arbalet-project/arbadoc/graphical_elements/background.JPG

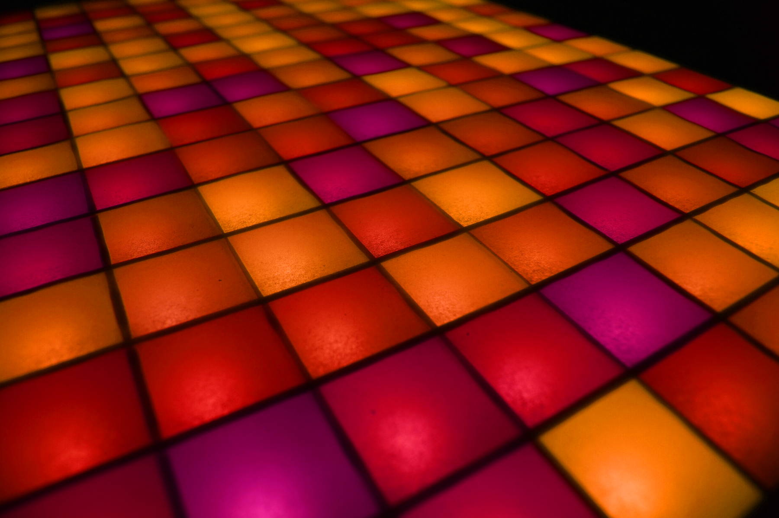
graphical_elements/background.JPG
