arbalet-project/arbadoc/graphical_elements/background_wide.jpg

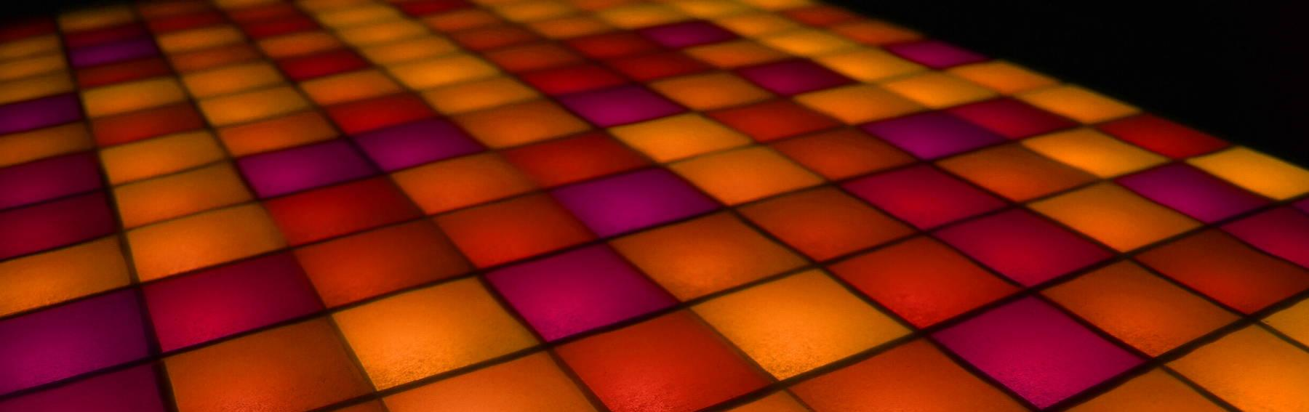
graphical_elements/background_wide.jpg
