arbalet-project/arbadoc/pics/collaborative_tetris.jpeg

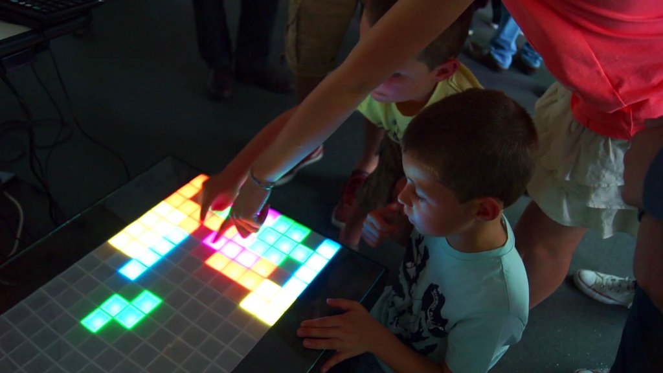
pics/collaborative_tetris.jpeg
