arbalet-project/arbadoc/pics/lights_hero.jpg

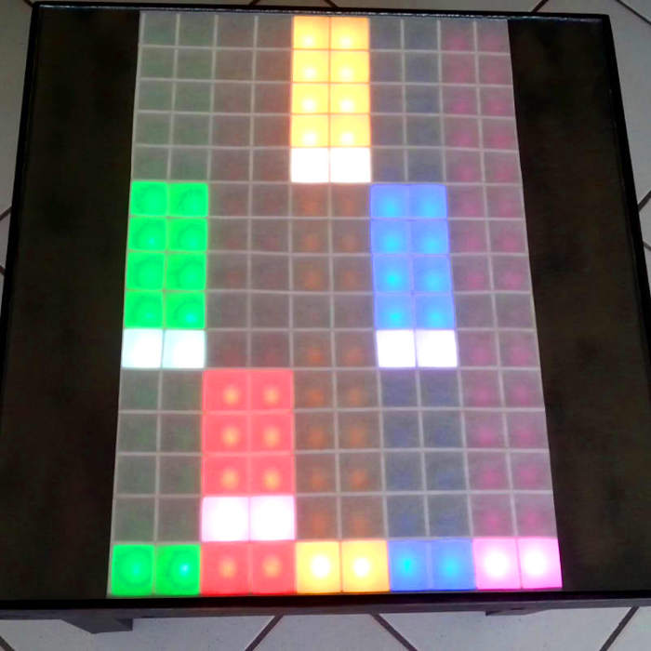
pics/lights_hero.jpg
