arbalet-project/arbadoc/pics/lights_hero_florian.jpg

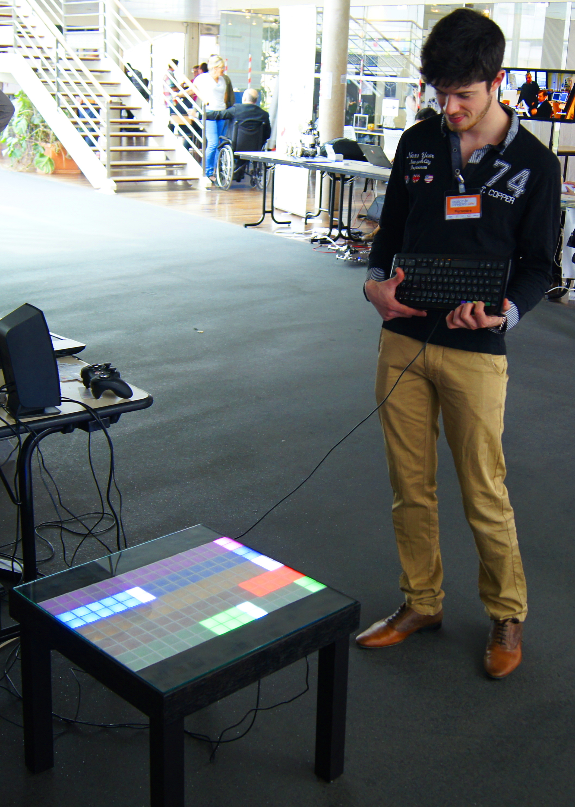
pics/lights_hero_florian.jpg
