arbalet-project/arbadoc/assembly_guidelines/lack/cad/Arbalet_TABLE_ASM.SLDASM

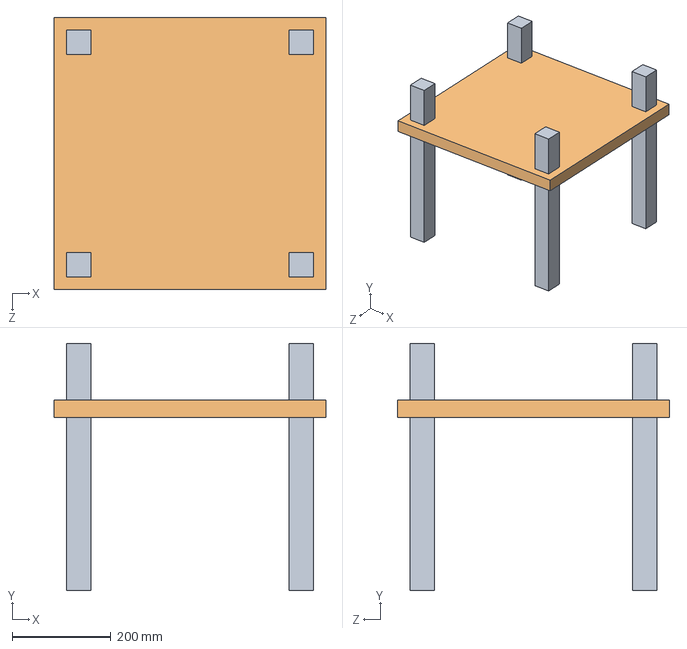
[picture p14: CAD file, 2015-10-09]
assembly_guidelines/lack/cad/Arbalet_TABLE_ASM.SLDASM
550.0 x 500.0 x 550.0 mm
Arbalet_TABLE_Tray
Arbalet_TABLE_LEG x 4
