arbalet-project/arbadoc/assembly_guidelines/lava/cad/host_box_grid_legs.fcstd

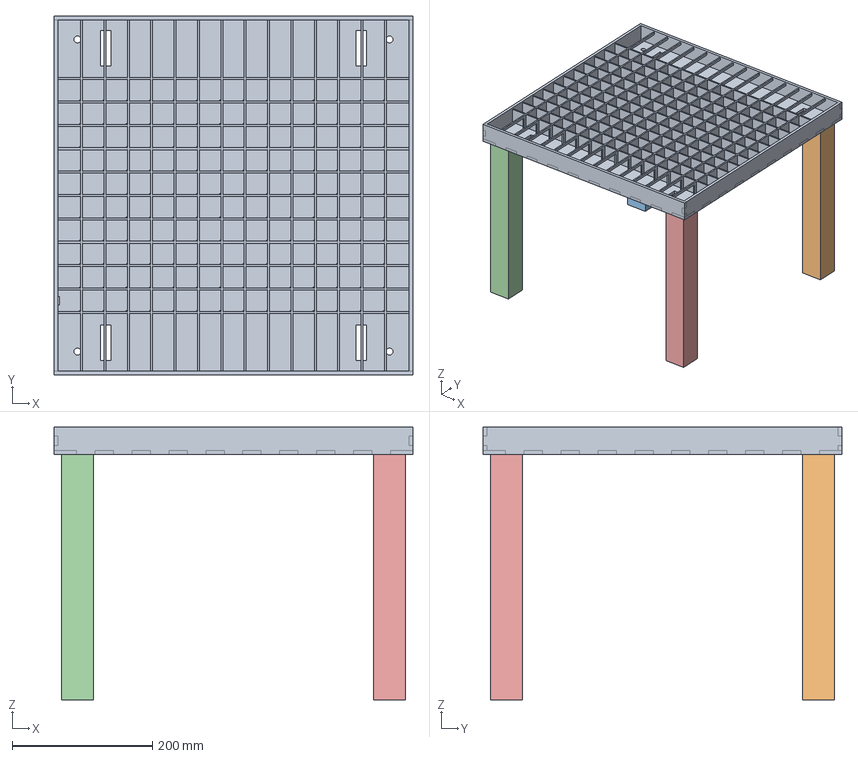
[picture p24: CAD file, 2016-04-23]
assembly_guidelines/lava/cad/host_box_grid_legs.fcstd
512.0 x 512.0 x 389.0 mm
host_box_grid_01
leg_01
leg_02
leg_03
leg_04
