arbalet-project/arbadoc/assembly_guidelines/lava/cad/leg.fcstd

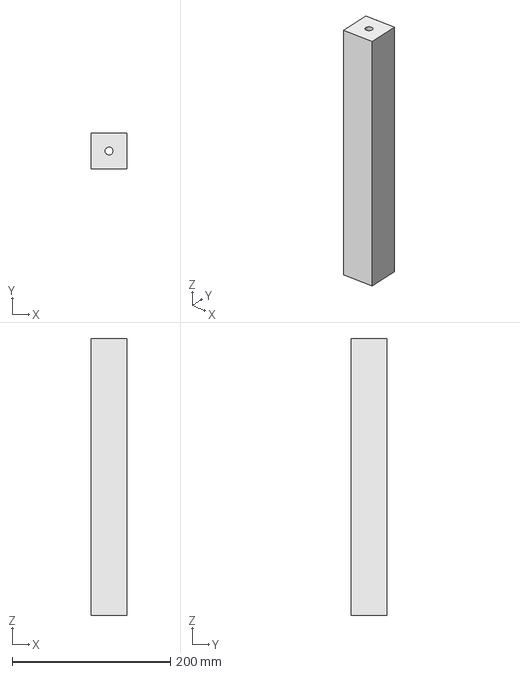
[picture p25: CAD file, 2016-03-13]
assembly_guidelines/lava/cad/leg.fcstd
45.0 x 45.0 x 350.0 mm
