arbalet-project/arbadoc/assembly_guidelines/lack/cad/Arbalet_GRID_Cover.SLDPRT

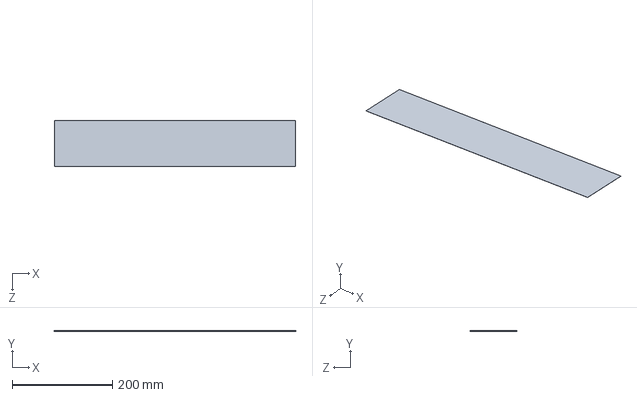
[picture p26: CAD file, 2015-10-09]
assembly_guidelines/lack/cad/Arbalet_GRID_Cover.SLDPRT
480.0 x 0.2 x 92.5 mm
