arbalet-project/arbadoc/assembly_guidelines/lava/cad/strip_333.fcstd

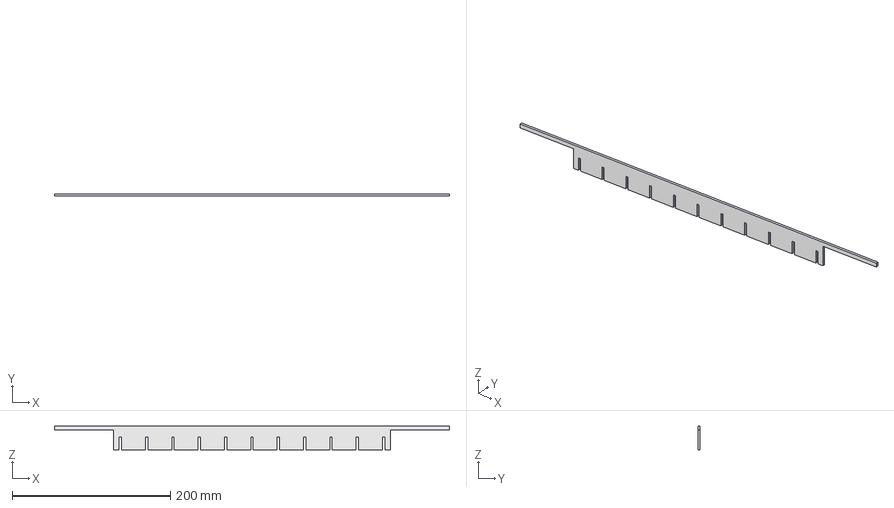
[picture p27: CAD file, 2016-03-13]
assembly_guidelines/lava/cad/strip_333.fcstd
500.0 x 3.00 x 30.0 mm
