arbalet-project/arbadoc/assembly_guidelines/lava/cad/strips_333.fcstd

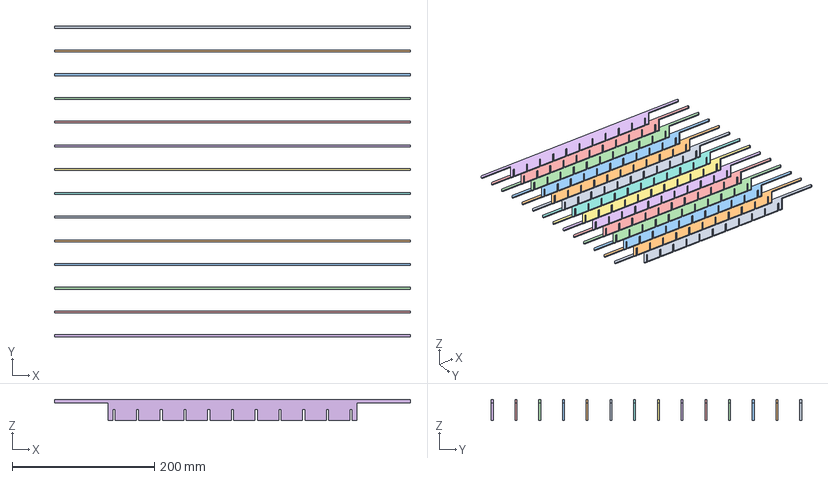
[picture p28: CAD file, 2016-03-13]
assembly_guidelines/lava/cad/strips_333.fcstd
500.0 x 436.3 x 30.0 mm
strip_333_01
strip_333_02
strip_333_03
strip_333_04
strip_333_05
strip_333_06
strip_333_07
strip_333_08
strip_333_09
strip_333_10
strip_333_11
strip_333_12
strip_333_13
strip_333_14
