arbalet-project/arbadoc/assembly_guidelines/lack/cad/Arbalet_GRID_Diffuser.SLDPRT

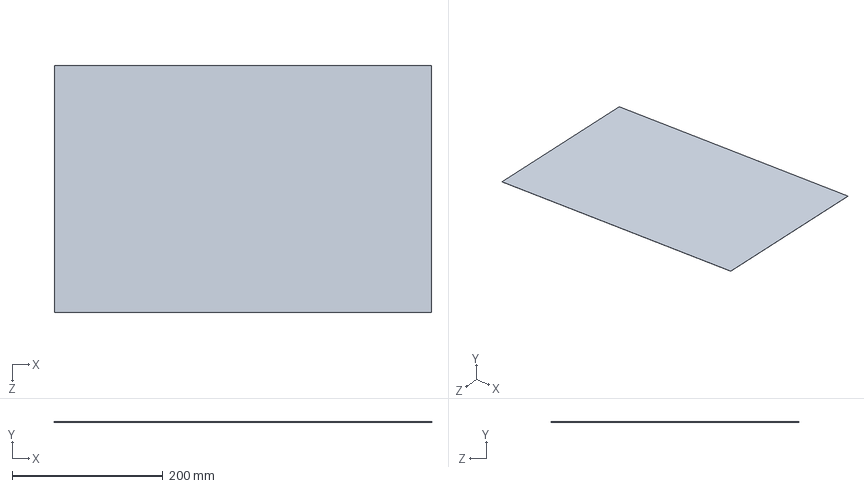
[picture p29: CAD file, 2015-10-09]
assembly_guidelines/lack/cad/Arbalet_GRID_Diffuser.SLDPRT
500.0 x 0.2 x 328.0 mm
