arbalet-project/arbadoc/assembly_guidelines/lava/cad/side_333.fcstd

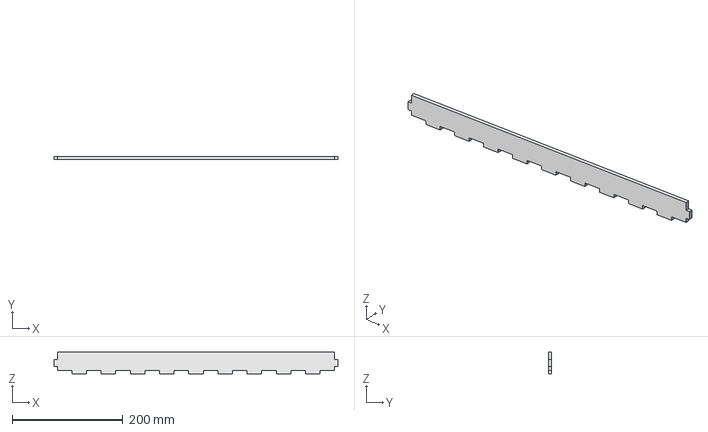
[picture p30: CAD file, 2016-03-13]
assembly_guidelines/lava/cad/side_333.fcstd
512.0 x 6.00 x 39.0 mm
