arbalet-project/arbadoc/assembly_guidelines/lack/cad/Arbalet_UPPER_TRAY_Frame.SLDPRT

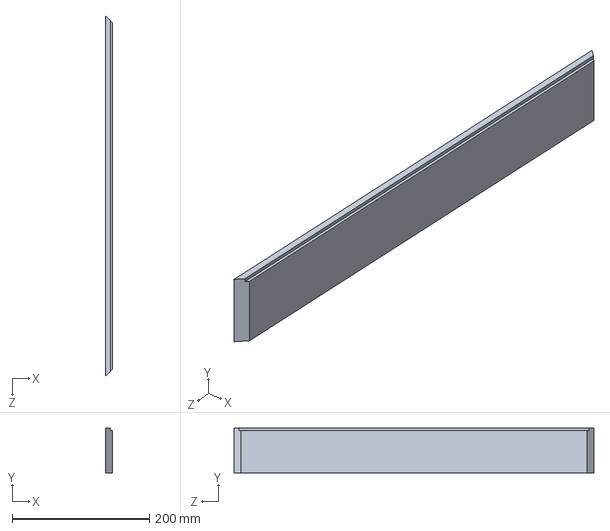
[picture p31: CAD file, 2015-10-09]
assembly_guidelines/lack/cad/Arbalet_UPPER_TRAY_Frame.SLDPRT
10.0 x 65.0 x 525.0 mm
