arbalet-project/arbadoc/assembly_guidelines/lack/cad/Arbalet_TABLE_Leg.SLDPRT

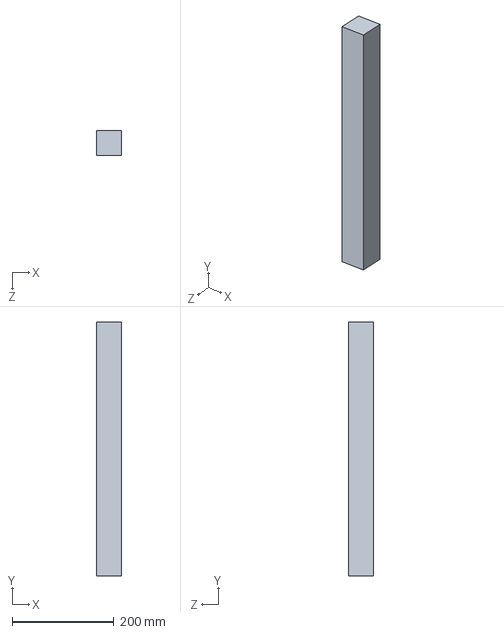
[picture p33: CAD file, 2015-10-09]
assembly_guidelines/lack/cad/Arbalet_TABLE_Leg.SLDPRT
50.0 x 500.0 x 50.0 mm
