arbalet-project/arbadoc/assembly_guidelines/lack/cad/Arbalet_ELECTRONIC_Tape.SLDPRT

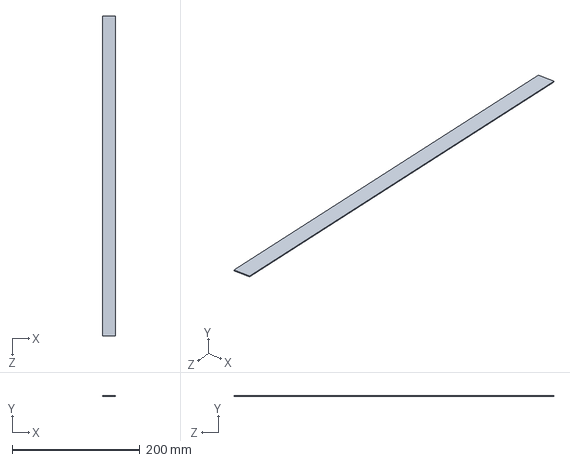
[picture p34: CAD file, 2015-10-09]
assembly_guidelines/lack/cad/Arbalet_ELECTRONIC_Tape.SLDPRT
20.0 x 1.00 x 500.0 mm
