arbalet-project/arbadoc/assembly_guidelines/lava/cad/bottom.fcstd

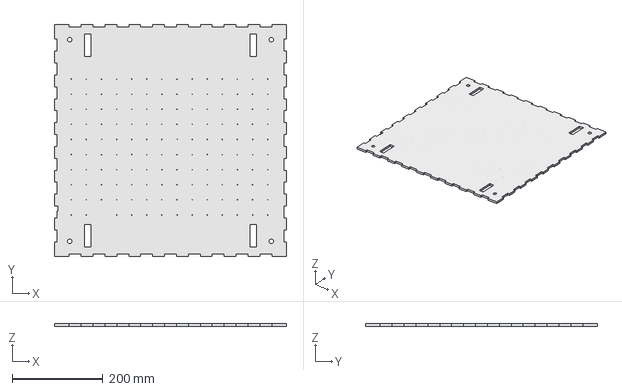
[picture p35: CAD file, 2016-03-13]
assembly_guidelines/lava/cad/bottom.fcstd
512.0 x 512.0 x 6.00 mm
