arbalet-project/arbadoc/assembly_guidelines/lava/cad/host_box.fcstd

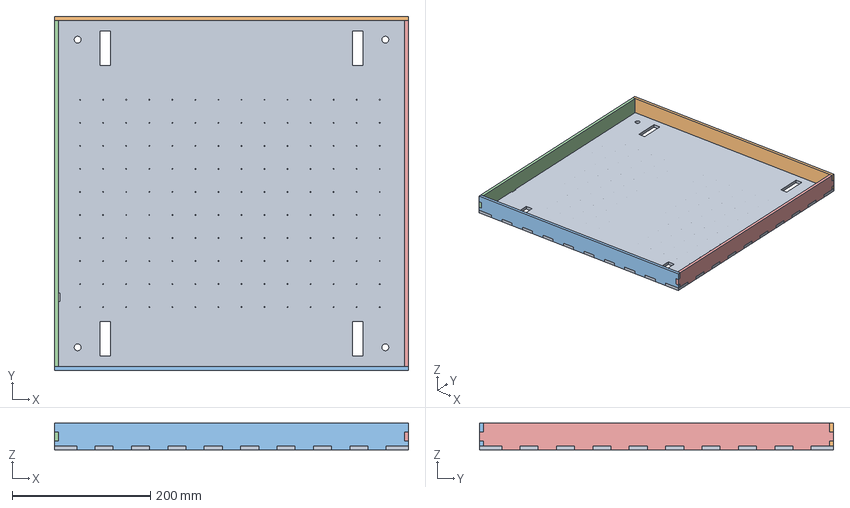
[picture p36: CAD file, 2016-03-13]
assembly_guidelines/lava/cad/host_box.fcstd
512.0 x 512.0 x 39.0 mm
bottom_01
side_500_01
side_500_02
side_333_01
side_333_02
