arbalet-project/arbadoc/assembly_guidelines/lava/cad/glass.fcstd

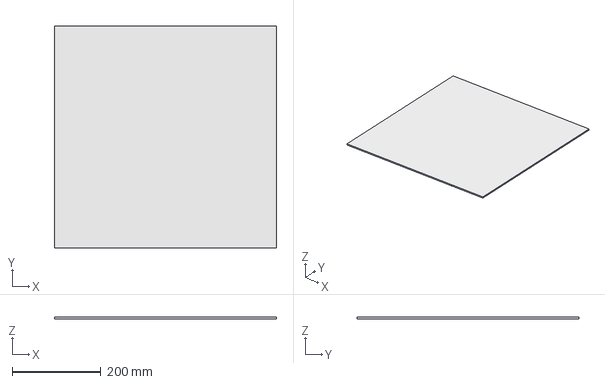
[picture p37: CAD file, 2016-02-26]
assembly_guidelines/lava/cad/glass.fcstd
500.0 x 500.0 x 4.00 mm
