arbalet-project/arbadoc/assembly_guidelines/lack/cad/preview.JPG

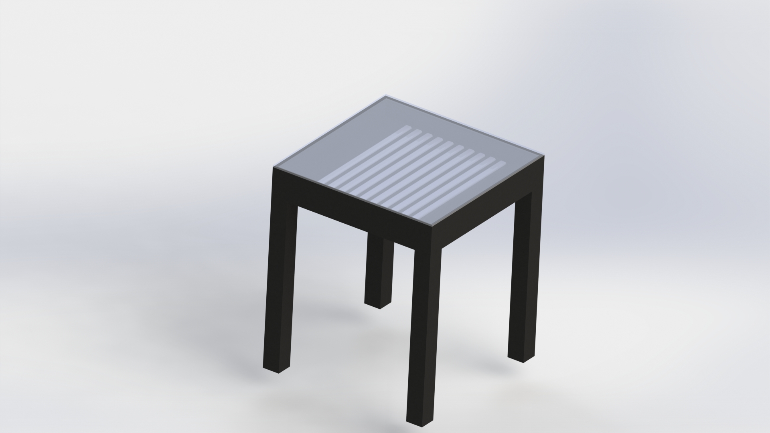
assembly_guidelines/lack/cad/preview.JPG
