arbalet-project/arbadoc/pics/build_1.jpeg

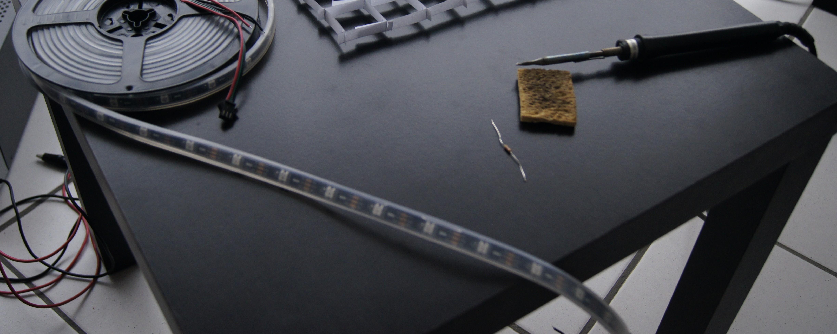
pics/build_1.jpeg
