arbalet-project/arbadoc/pics/build_3.jpeg

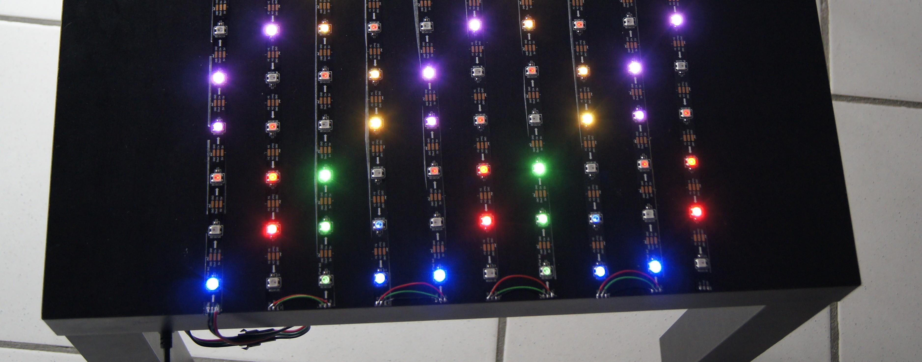
pics/build_3.jpeg
