arbalet-project/arbadoc/pics/build_6.jpeg

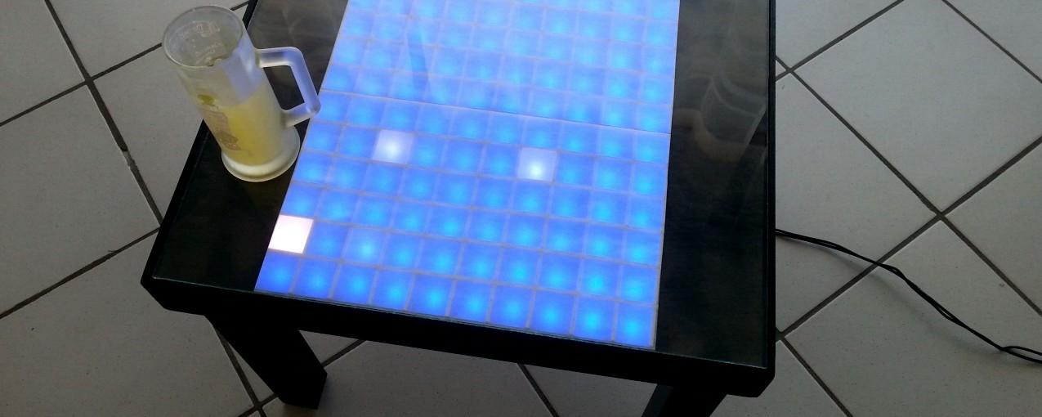
pics/build_6.jpeg
